antiank4/SniffKitty--ODOR-SENSOR/include/camera_server.h

#ifndef CAMERA_SERVER_H
#define CAMERA_SERVER_H

void initCamera();
void connectWiFi();
void startCameraServer();
void captureCameraBaselineAfterDelay();
String capturePresencePhotoToSD();
bool updateCameraPresence();

extern bool cameraBaselineReady;
extern bool currentCameraPresent;
extern float currentCameraChangePercent;
extern bool currentCameraBoxValid;
extern float currentCameraBoxXPercent;
extern float currentCameraBoxYPercent;
extern float currentCameraBoxWPercent;
extern float currentCameraBoxHPercent;

#endif
