antiank4/SniffKitty--ODOR-SENSOR/include/wifi_credentials.example.h

#ifndef WIFI_CREDENTIALS_EXAMPLE_H
#define WIFI_CREDENTIALS_EXAMPLE_H

// Copy this file to include/wifi_credentials.h and fill in your real values.
// Leave WIFI_PASSWORD empty when using eduroam / WPA Enterprise.

#define WIFI_SSID "eduroam"
#define WIFI_PASSWORD ""
#define WIFI_ENTERPRISE_USERNAME "your_ucsd_username"
#define WIFI_ENTERPRISE_PASSWORD "your_ucsd_password"

#endif
